PeterSimpsonYoung/Smartphone-Ophthalmoscope-Project/Testing/NormalImage/Im020.jpg

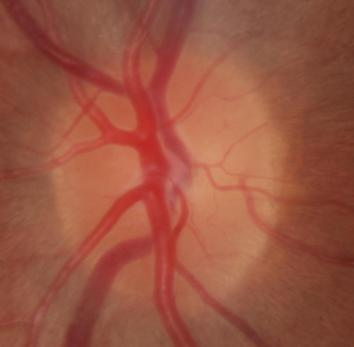
Testing/NormalImage/Im020.jpg
