PeterSimpsonYoung/Smartphone-Ophthalmoscope-Project/Testing/NormalImage/Im038.jpg

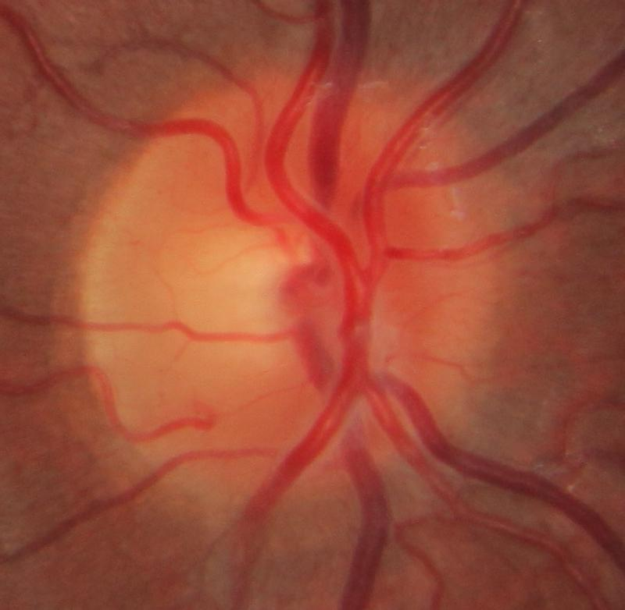
Testing/NormalImage/Im038.jpg
