PeterSimpsonYoung/Smartphone-Ophthalmoscope-Project/3D models/ophthalmoscope_lid_v02.png

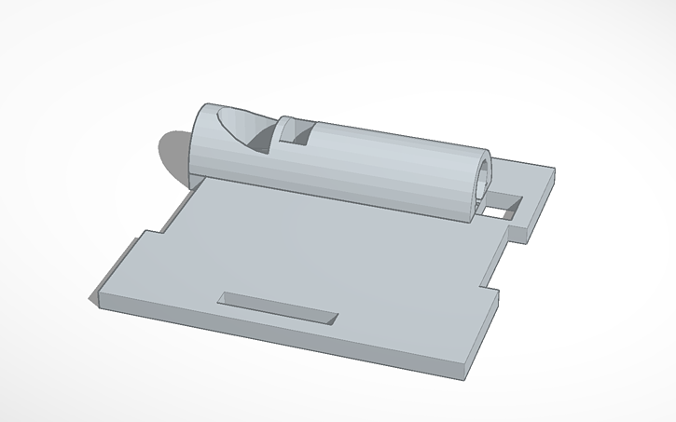
3D models/ophthalmoscope_lid_v02.png
