PeterSimpsonYoung/Smartphone-Ophthalmoscope-Project/Input/Im114.jpg

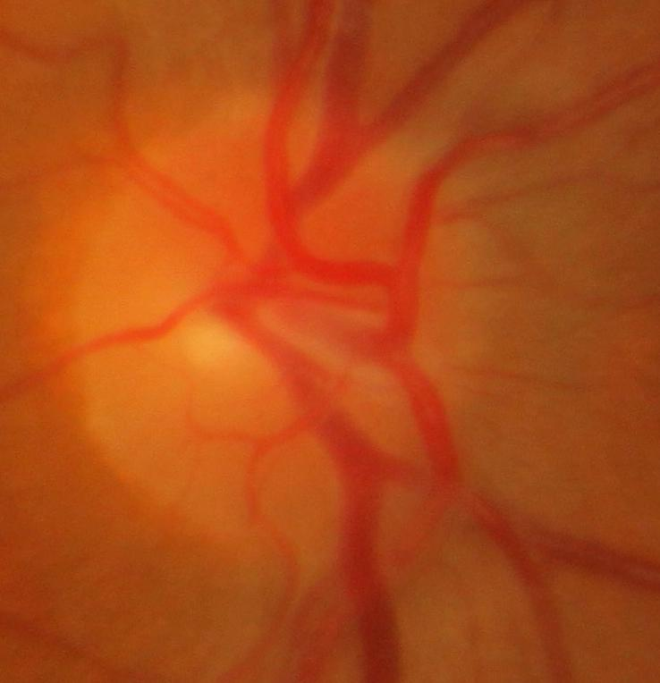
Input/Im114.jpg
