PeterSimpsonYoung/Smartphone-Ophthalmoscope-Project/Input/Im256.jpg

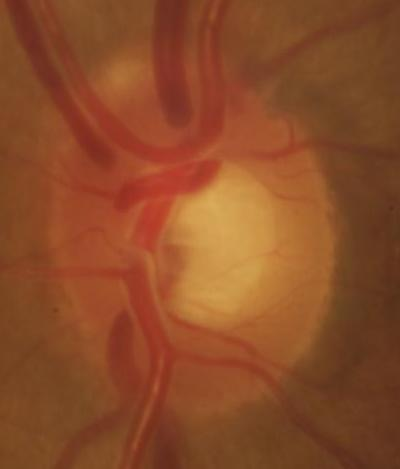
Input/Im256.jpg
