PeterSimpsonYoung/Smartphone-Ophthalmoscope-Project/Input/Im257.jpg

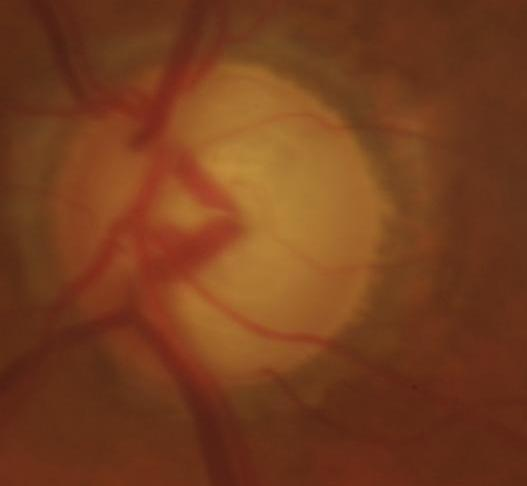
Input/Im257.jpg
