PeterSimpsonYoung/Smartphone-Ophthalmoscope-Project/Input/Im258.jpg

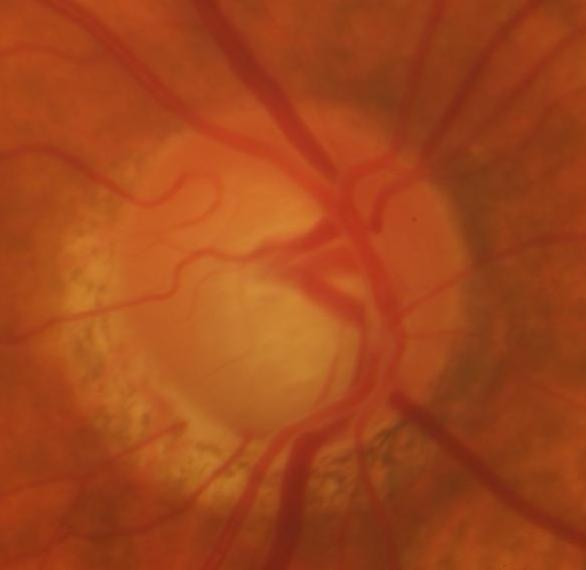
Input/Im258.jpg
