PeterSimpsonYoung/Smartphone-Ophthalmoscope-Project/Input/Im259.jpg

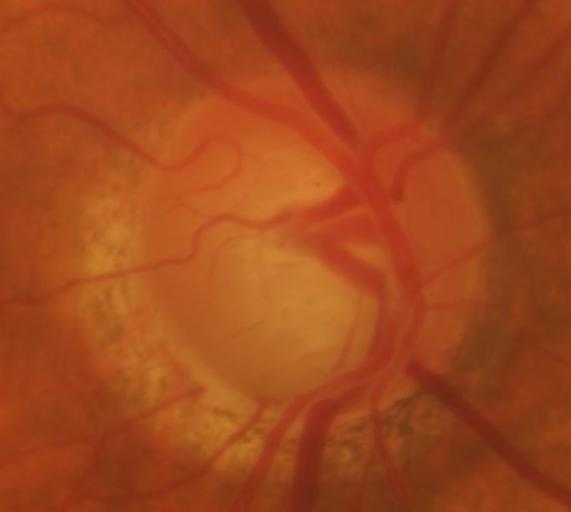
Input/Im259.jpg
