PeterSimpsonYoung/Smartphone-Ophthalmoscope-Project/Input/Im260.jpg

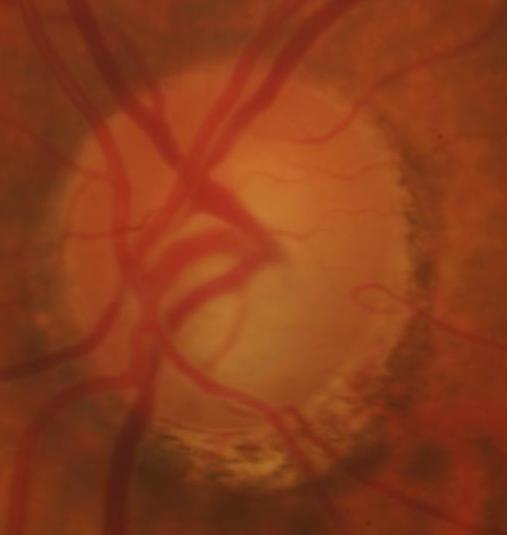
Input/Im260.jpg
