PeterSimpsonYoung/Smartphone-Ophthalmoscope-Project/Input/Im261.jpg

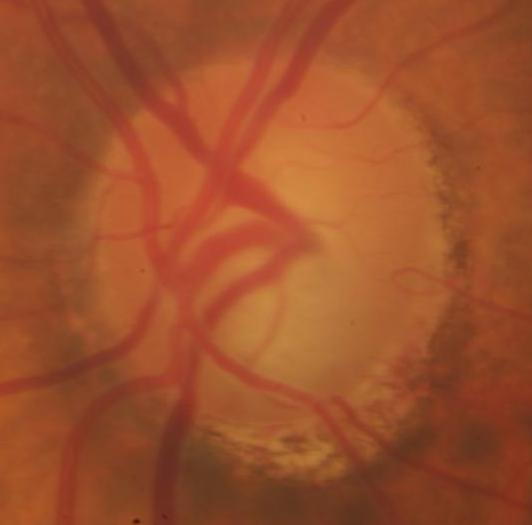
Input/Im261.jpg
