PeterSimpsonYoung/Smartphone-Ophthalmoscope-Project/Input/Im262.jpg

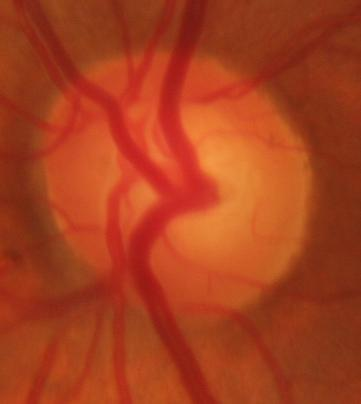
Input/Im262.jpg
