PeterSimpsonYoung/Smartphone-Ophthalmoscope-Project/Input/Im263.jpg

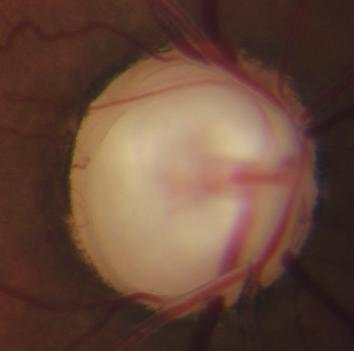
Input/Im263.jpg
