PeterSimpsonYoung/Smartphone-Ophthalmoscope-Project/Input/Im321.jpg

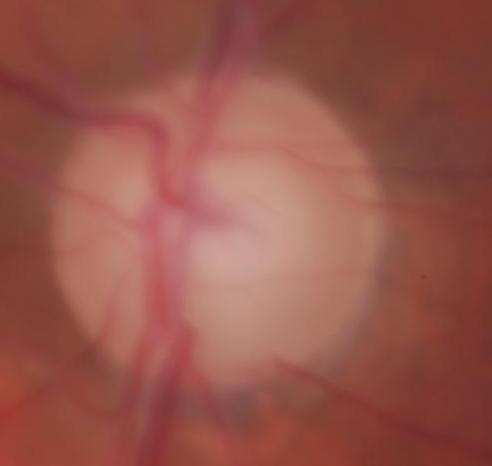
Input/Im321.jpg
