PeterSimpsonYoung/Smartphone-Ophthalmoscope-Project/Testing/NormalImage/Im001.jpg

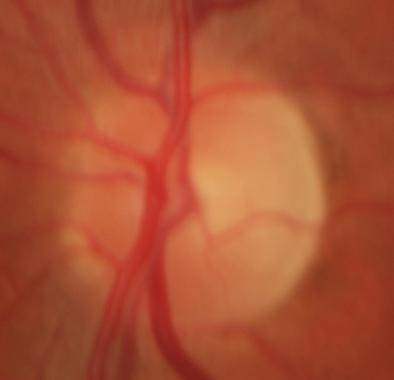
Testing/NormalImage/Im001.jpg
