PeterSimpsonYoung/Smartphone-Ophthalmoscope-Project/Testing/NormalImage/Im002.jpg

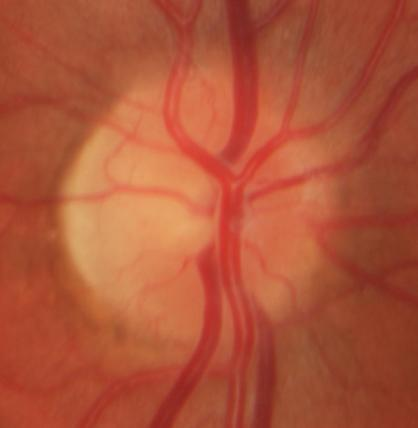
Testing/NormalImage/Im002.jpg
