PeterSimpsonYoung/Smartphone-Ophthalmoscope-Project/Testing/NormalImage/Im003.jpg

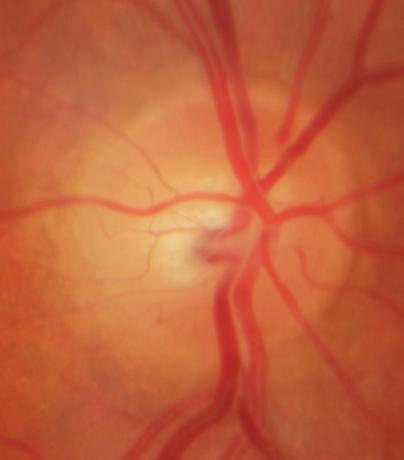
Testing/NormalImage/Im003.jpg
