PeterSimpsonYoung/Smartphone-Ophthalmoscope-Project/Testing/NormalImage/Im004.jpg

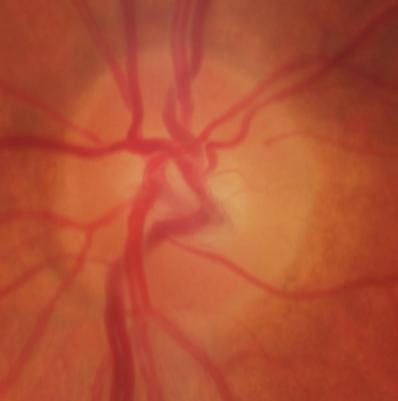
Testing/NormalImage/Im004.jpg
