PeterSimpsonYoung/Smartphone-Ophthalmoscope-Project/Testing/NormalImage/Im005.jpg

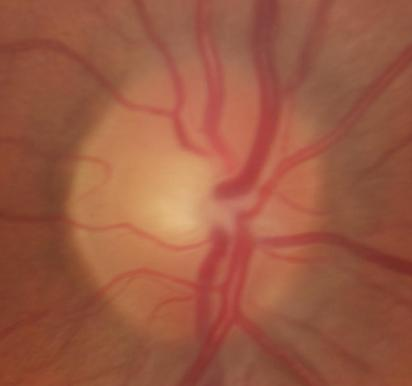
Testing/NormalImage/Im005.jpg
