PeterSimpsonYoung/Smartphone-Ophthalmoscope-Project/Testing/NormalImage/Im006.jpg

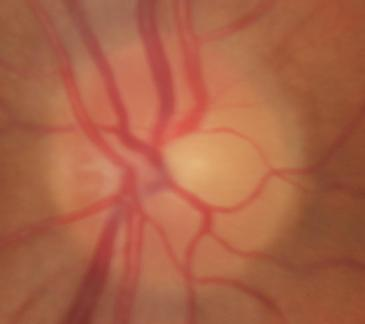
Testing/NormalImage/Im006.jpg
