PeterSimpsonYoung/Smartphone-Ophthalmoscope-Project/Testing/NormalImage/Im007.jpg

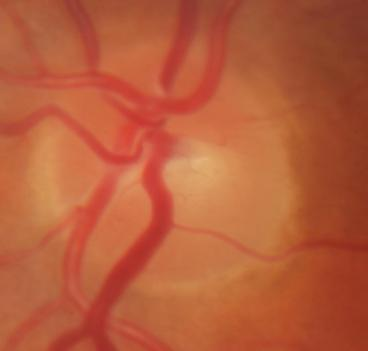
Testing/NormalImage/Im007.jpg
