PeterSimpsonYoung/Smartphone-Ophthalmoscope-Project/Testing/NormalImage/Im008.jpg

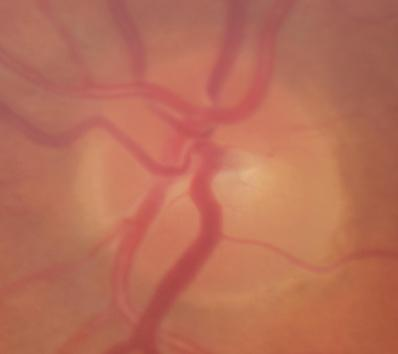
Testing/NormalImage/Im008.jpg
