PeterSimpsonYoung/Smartphone-Ophthalmoscope-Project/Testing/NormalImage/Im009.jpg

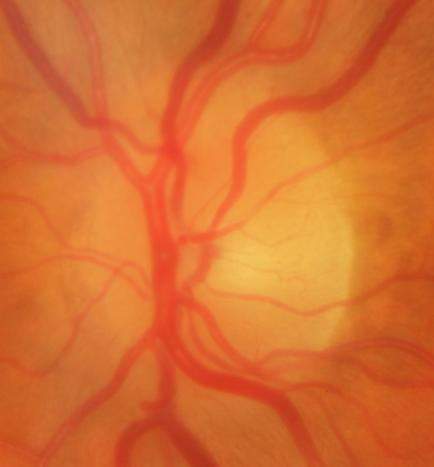
Testing/NormalImage/Im009.jpg
