PeterSimpsonYoung/Smartphone-Ophthalmoscope-Project/Testing/NormalImage/Im010.jpg

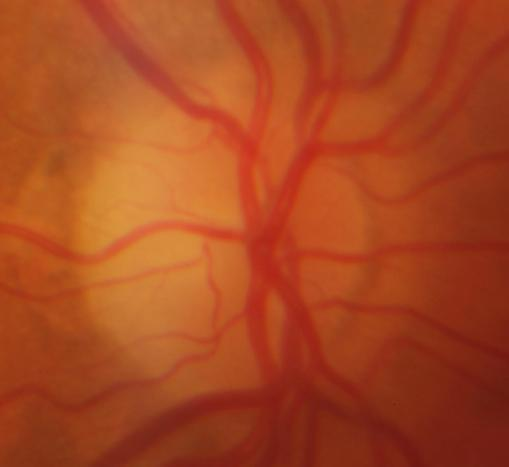
Testing/NormalImage/Im010.jpg
