PeterSimpsonYoung/Smartphone-Ophthalmoscope-Project/Testing/NormalImage/Im011.jpg

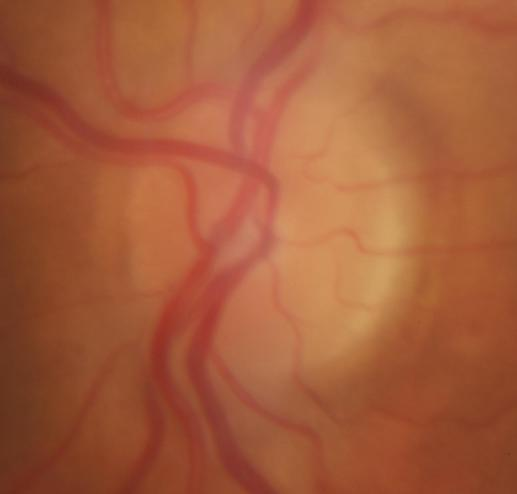
Testing/NormalImage/Im011.jpg
