PeterSimpsonYoung/Smartphone-Ophthalmoscope-Project/Testing/NormalImage/Im012.jpg

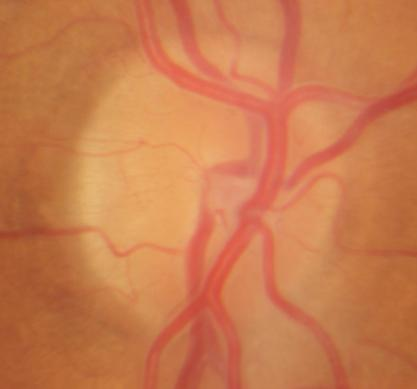
Testing/NormalImage/Im012.jpg
