PeterSimpsonYoung/Smartphone-Ophthalmoscope-Project/Testing/NormalImage/Im013.jpg

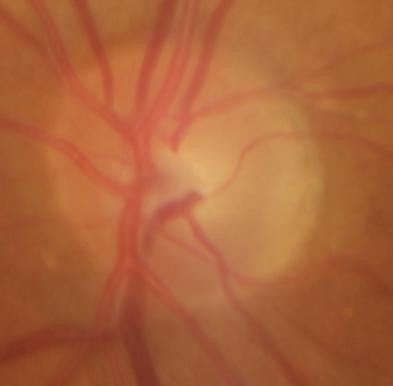
Testing/NormalImage/Im013.jpg
