PeterSimpsonYoung/Smartphone-Ophthalmoscope-Project/Testing/NormalImage/Im014.jpg

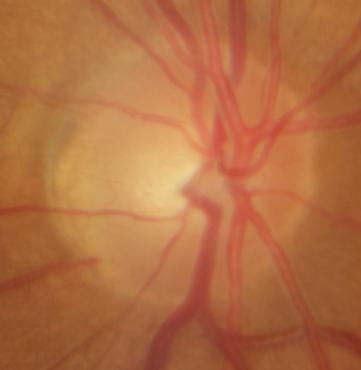
Testing/NormalImage/Im014.jpg
