PeterSimpsonYoung/Smartphone-Ophthalmoscope-Project/Testing/NormalImage/Im015.jpg

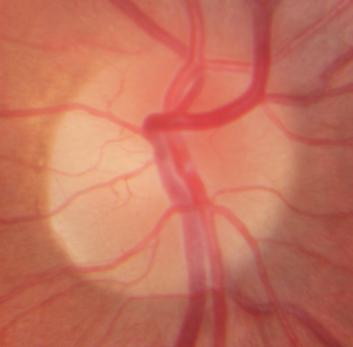
Testing/NormalImage/Im015.jpg
