PeterSimpsonYoung/Smartphone-Ophthalmoscope-Project/Testing/NormalImage/Im016.jpg

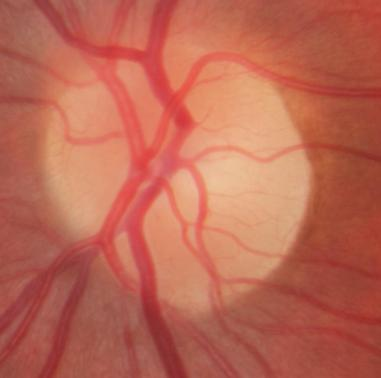
Testing/NormalImage/Im016.jpg
