PeterSimpsonYoung/Smartphone-Ophthalmoscope-Project/Testing/NormalImage/Im017.jpg

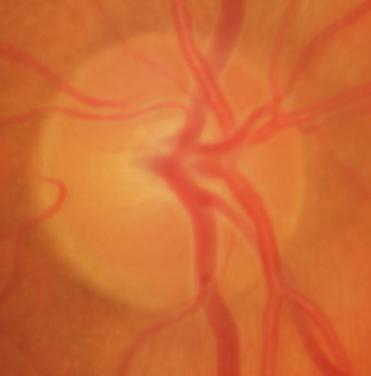
Testing/NormalImage/Im017.jpg
