PeterSimpsonYoung/Smartphone-Ophthalmoscope-Project/Testing/NormalImage/Im018.jpg

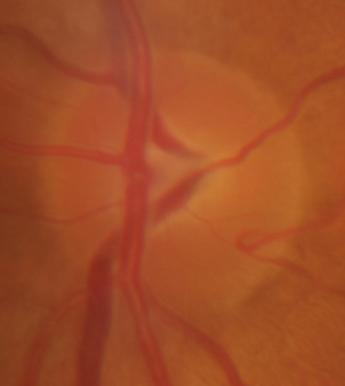
Testing/NormalImage/Im018.jpg
