PeterSimpsonYoung/Smartphone-Ophthalmoscope-Project/Testing/NormalImage/Im019.jpg

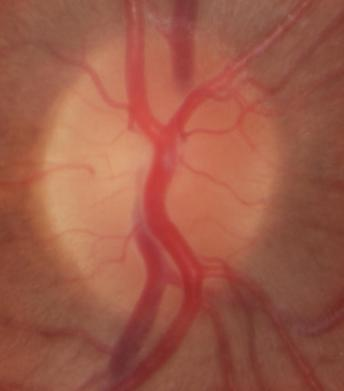
Testing/NormalImage/Im019.jpg
