PeterSimpsonYoung/Smartphone-Ophthalmoscope-Project/Testing/NormalImage/Im021.jpg

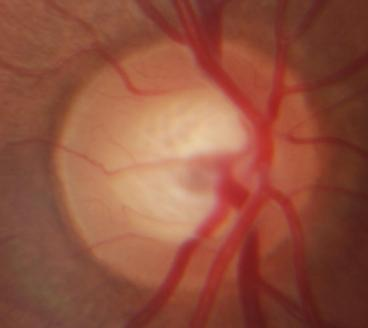
Testing/NormalImage/Im021.jpg
