PeterSimpsonYoung/Smartphone-Ophthalmoscope-Project/Testing/NormalImage/Im022.jpg

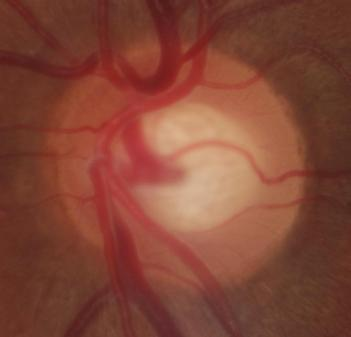
Testing/NormalImage/Im022.jpg
