PeterSimpsonYoung/Smartphone-Ophthalmoscope-Project/Testing/NormalImage/Im023.jpg

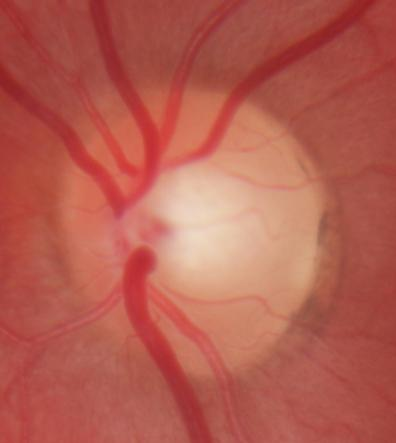
Testing/NormalImage/Im023.jpg
