PeterSimpsonYoung/Smartphone-Ophthalmoscope-Project/Testing/NormalImage/Im024.jpg

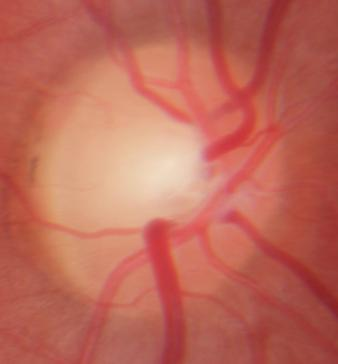
Testing/NormalImage/Im024.jpg
