PeterSimpsonYoung/Smartphone-Ophthalmoscope-Project/Testing/NormalImage/Im025.jpg

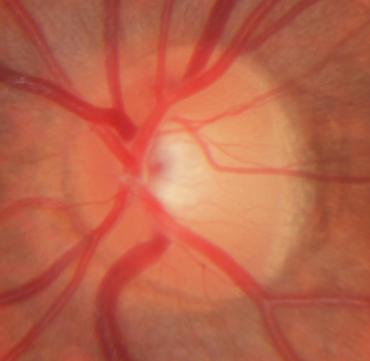
Testing/NormalImage/Im025.jpg
