PeterSimpsonYoung/Smartphone-Ophthalmoscope-Project/Testing/NormalImage/Im026.jpg

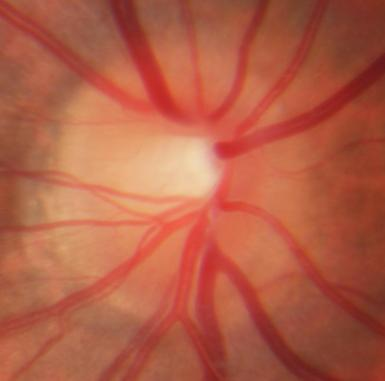
Testing/NormalImage/Im026.jpg
