PeterSimpsonYoung/Smartphone-Ophthalmoscope-Project/Testing/NormalImage/Im027.jpg

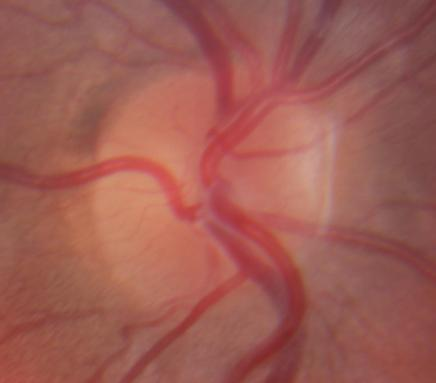
Testing/NormalImage/Im027.jpg
