PeterSimpsonYoung/Smartphone-Ophthalmoscope-Project/Testing/NormalImage/Im028.jpg

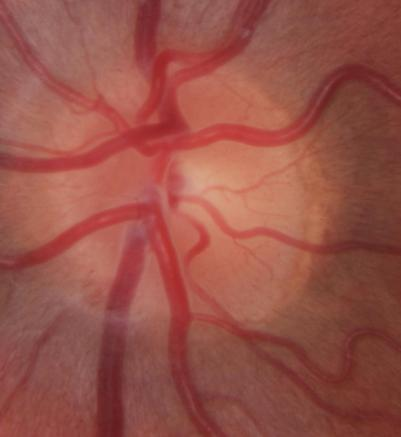
Testing/NormalImage/Im028.jpg
