PeterSimpsonYoung/Smartphone-Ophthalmoscope-Project/Testing/NormalImage/Im029.jpg

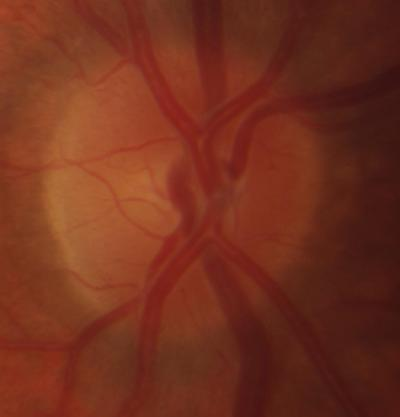
Testing/NormalImage/Im029.jpg
