PeterSimpsonYoung/Smartphone-Ophthalmoscope-Project/Testing/NormalImage/Im030.jpg

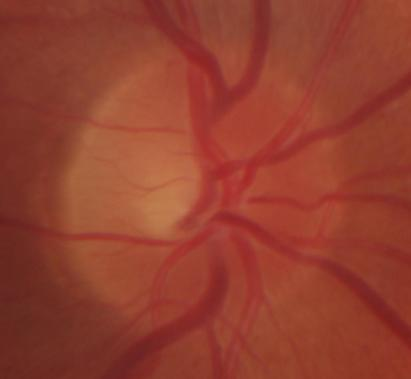
Testing/NormalImage/Im030.jpg
