PeterSimpsonYoung/Smartphone-Ophthalmoscope-Project/Testing/NormalImage/Im031.jpg

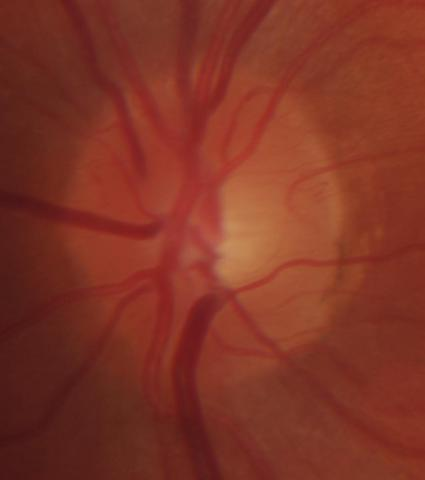
Testing/NormalImage/Im031.jpg
