PeterSimpsonYoung/Smartphone-Ophthalmoscope-Project/Testing/NormalImage/Im032.jpg

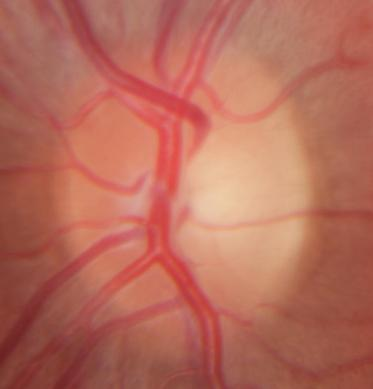
Testing/NormalImage/Im032.jpg
