PeterSimpsonYoung/Smartphone-Ophthalmoscope-Project/Testing/NormalImage/Im033.jpg

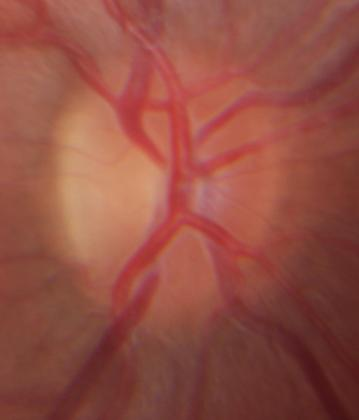
Testing/NormalImage/Im033.jpg
