PeterSimpsonYoung/Smartphone-Ophthalmoscope-Project/Testing/NormalImage/Im034.jpg

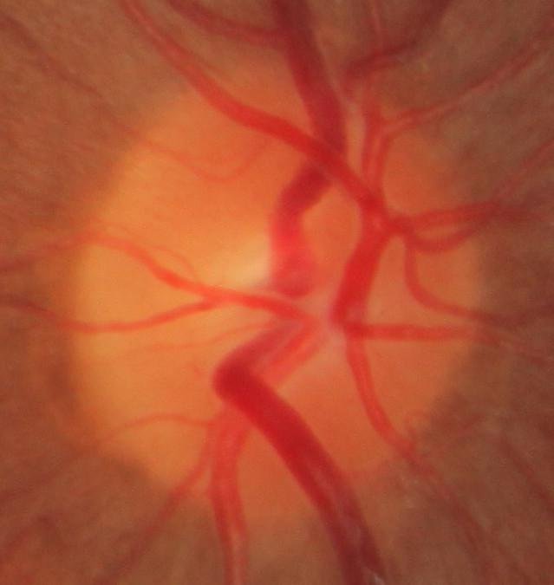
Testing/NormalImage/Im034.jpg
