PeterSimpsonYoung/Smartphone-Ophthalmoscope-Project/Testing/NormalImage/Im035.jpg

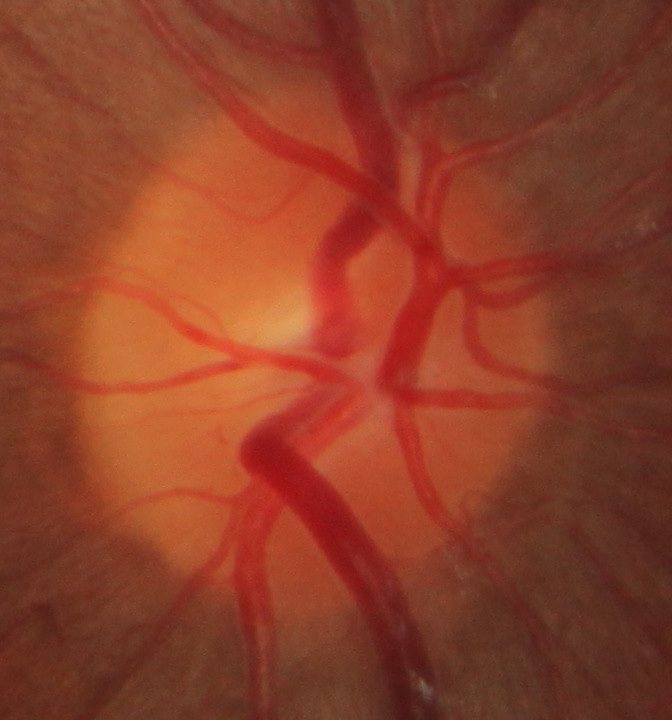
Testing/NormalImage/Im035.jpg
