PeterSimpsonYoung/Smartphone-Ophthalmoscope-Project/Testing/NormalImage/Im036.jpg

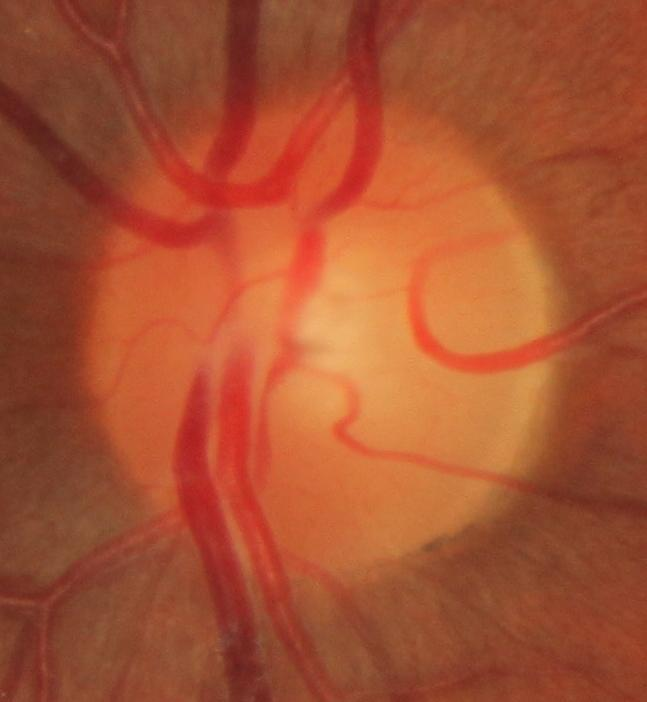
Testing/NormalImage/Im036.jpg
