PeterSimpsonYoung/Smartphone-Ophthalmoscope-Project/Testing/NormalImage/Im039.jpg

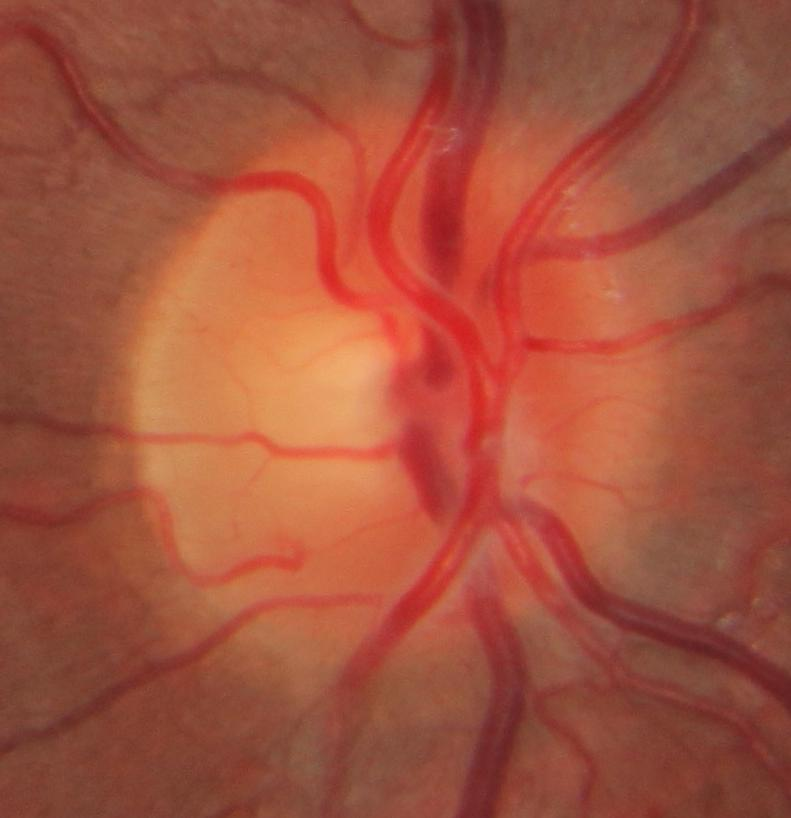
Testing/NormalImage/Im039.jpg
