PeterSimpsonYoung/Smartphone-Ophthalmoscope-Project/Testing/NormalImage/Im040.jpg

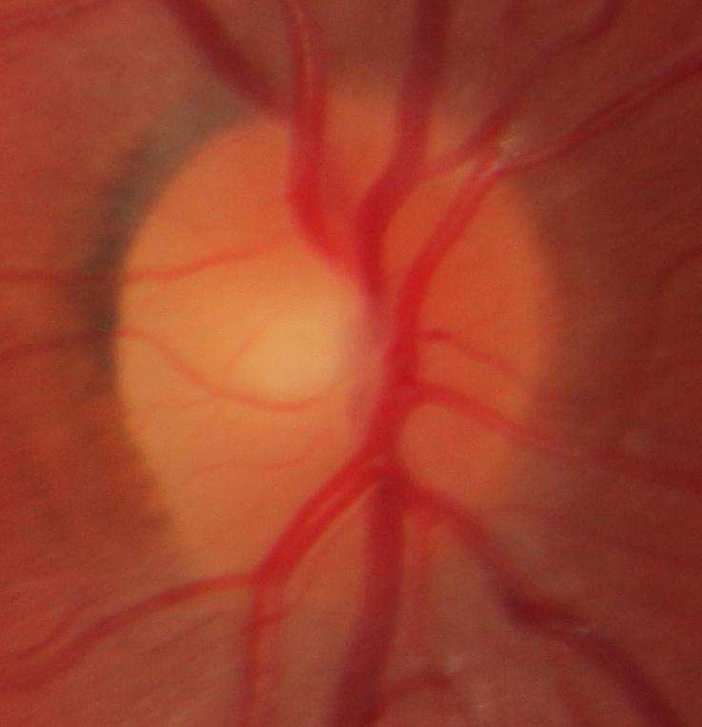
Testing/NormalImage/Im040.jpg
