PeterSimpsonYoung/Smartphone-Ophthalmoscope-Project/Testing/NormalImage/Im042.jpg

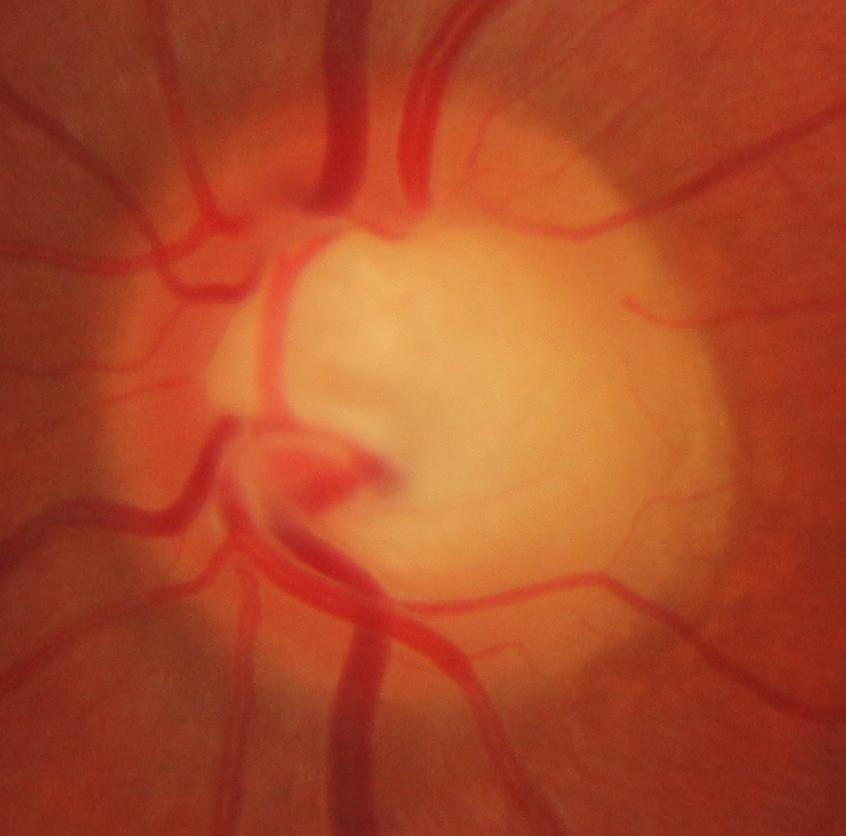
Testing/NormalImage/Im042.jpg
