PeterSimpsonYoung/Smartphone-Ophthalmoscope-Project/Testing/NormalImage/Im043.jpg

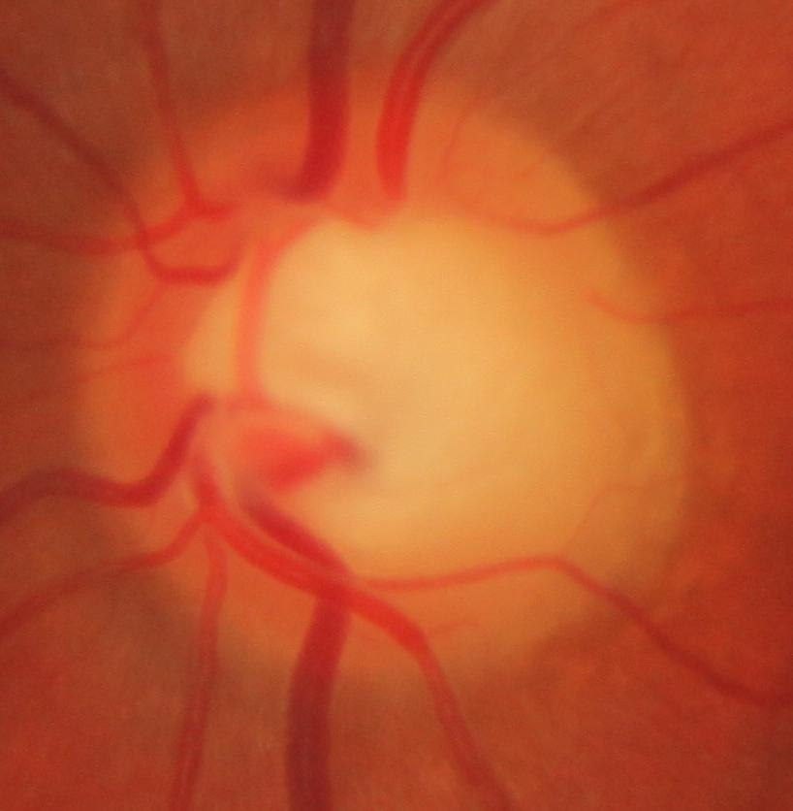
Testing/NormalImage/Im043.jpg
