PeterSimpsonYoung/Smartphone-Ophthalmoscope-Project/Testing/NormalImage/Im044.jpg

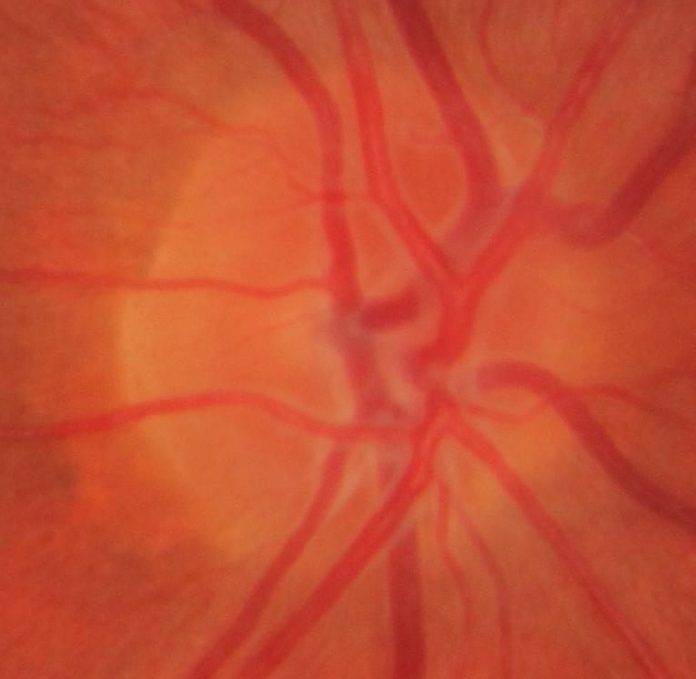
Testing/NormalImage/Im044.jpg
