PeterSimpsonYoung/Smartphone-Ophthalmoscope-Project/Testing/NormalImage/Im045.jpg

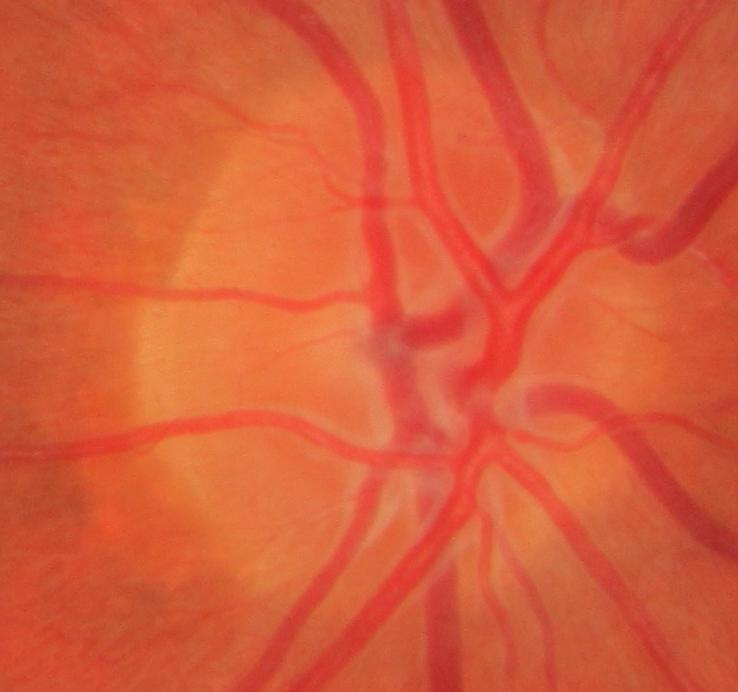
Testing/NormalImage/Im045.jpg
