PeterSimpsonYoung/Smartphone-Ophthalmoscope-Project/Testing/NormalImage/Im046.jpg

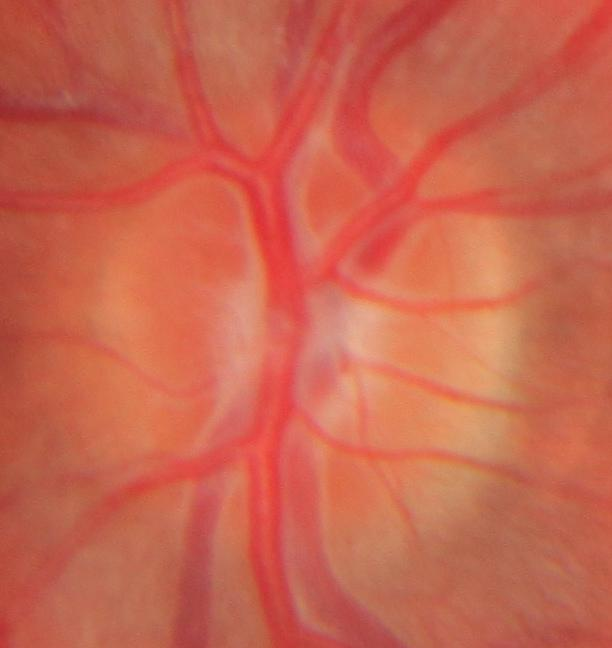
Testing/NormalImage/Im046.jpg
