PeterSimpsonYoung/Smartphone-Ophthalmoscope-Project/Testing/NormalImage/Im047.jpg

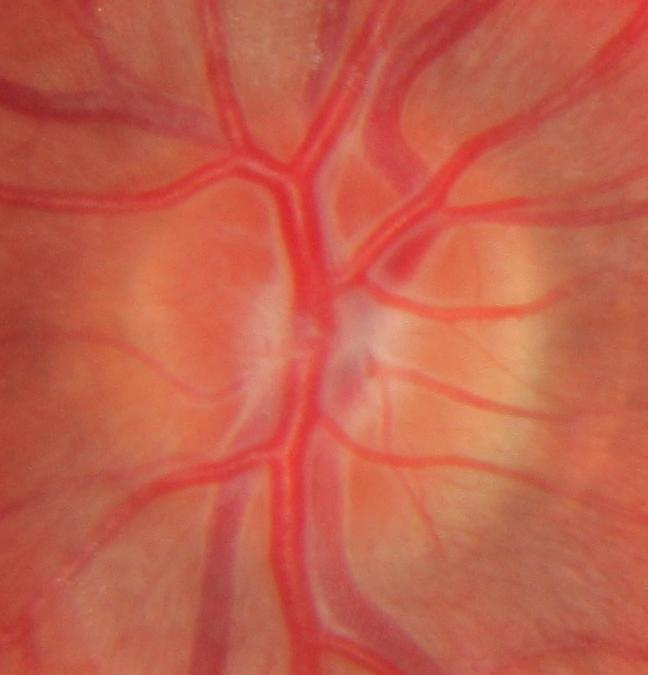
Testing/NormalImage/Im047.jpg
