PeterSimpsonYoung/Smartphone-Ophthalmoscope-Project/Testing/NormalImage/Im048.jpg

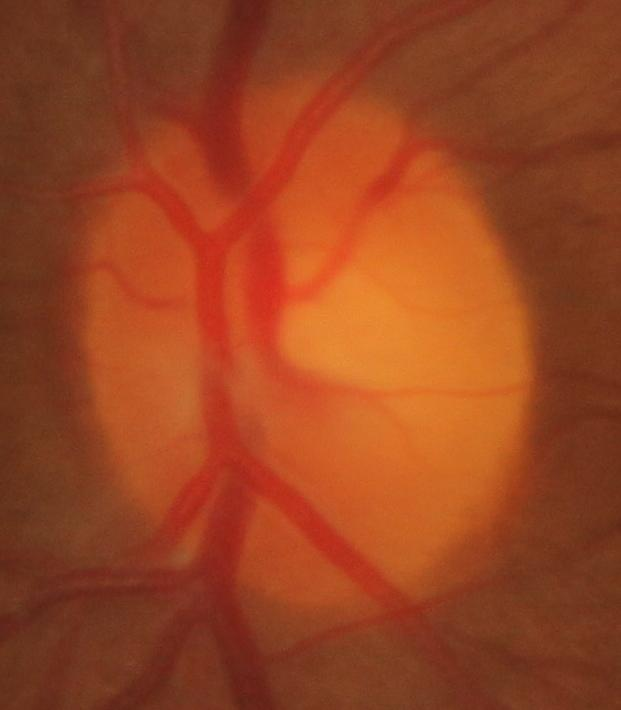
Testing/NormalImage/Im048.jpg
